Kraben/act-labs-ps1-bluetooth/ACT_Labs_REX.kicad_sch

## KiCad design ACT_Labs_REX.kicad_sch (2026-06-24)

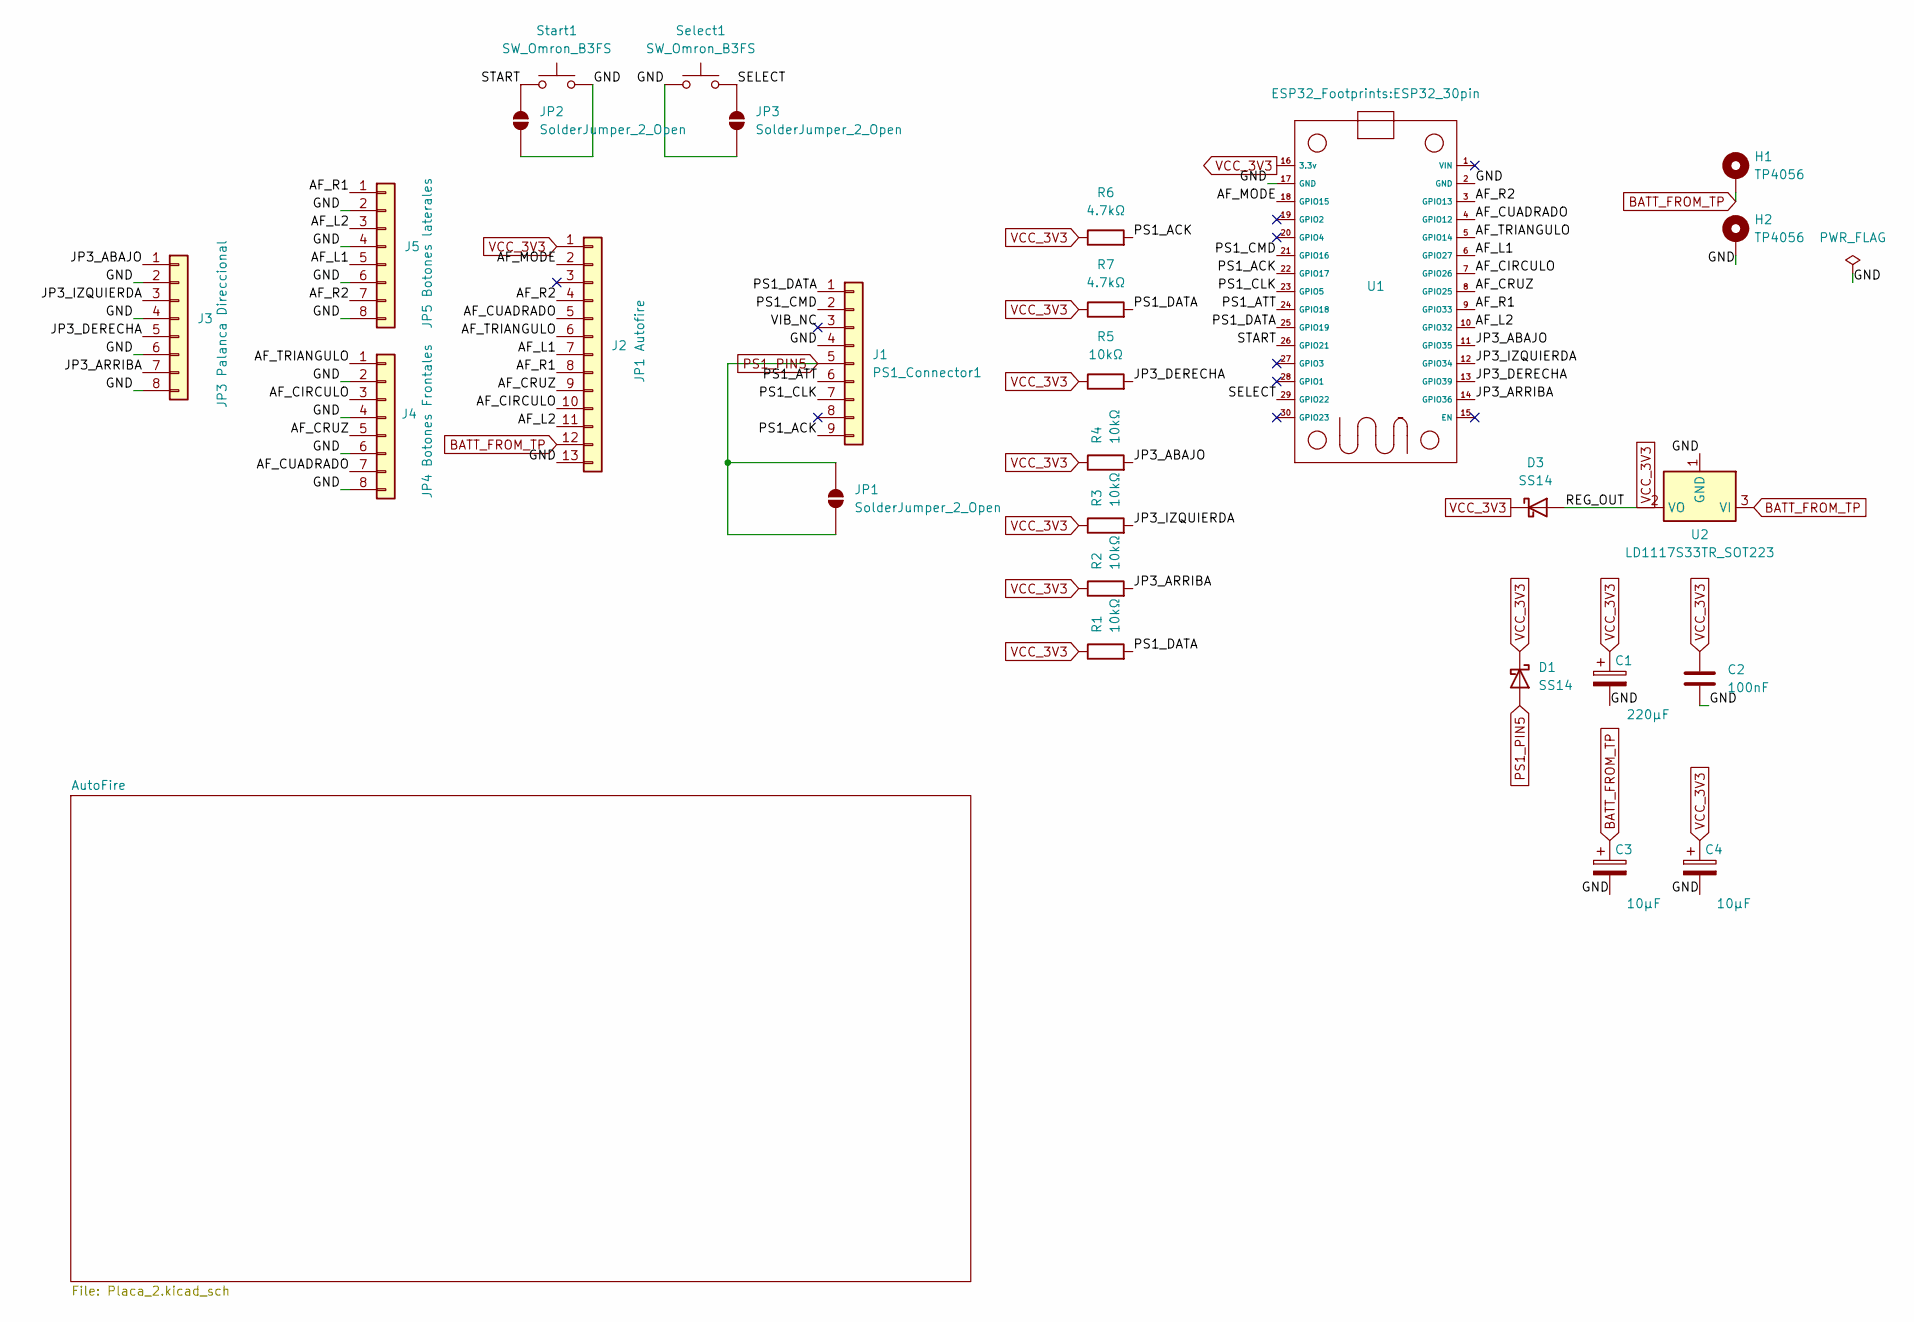
[picture p20: schematic ACT_Labs_REX.kicad_sch]

Parts:
C1: 220µF; CP_Radial_D6.3mm_P2.50mm
C2: 100nF; C_Disc_D3.0mm_W1.6mm_P2.50mm
C3, C4: 10µF; CP_Radial_D6.3mm_P2.50mm
D1, D3: SS14; D_SMA
H1, H2: TP4056; MountingHole_2.5mm_Pad
J1: PS1_Connector1; PinHeader_1x09_P2.54mm_Vertical
J2: JP1 Autofire; PinHeader_1x13_P2.54mm_Vertical
J3: JP3 Palanca Direccional; PinHeader_1x08_P2.54mm_Vertical
J4: JP4 Botones Frontales; PinHeader_1x08_P2.54mm_Vertical
J5: JP5 Botones laterales; PinHeader_1x08_P2.54mm_Vertical
JP1, JP2, JP3: SolderJumper_2_Open; SolderJumper-2_P1.3mm_Open_TrianglePad1.0x1.5mm
R1, R2, R3, R4, R5: 10kΩ; R_Axial_DIN0207_L6.3mm_D2.5mm_P7.62mm_Horizontal
R6, R7: 4.7kΩ; R_Axial_DIN0207_L6.3mm_D2.5mm_P7.62mm_Horizontal
Select1: SW_Omron_B3FS; SW_SPST_Omron_B3F-50xx
Start1: SW_Omron_B3FS; SW_SPST_Omron_B3F-50xx
U1: ESP32_30pin
U2: LD1117S33TR_SOT223; SOT-223-3_TabPin2

Connections:
AF_CIRCULO: J2.10, J4.3, U1.7 (GPIO26)
AF_CRUZ: J2.9, J4.5, U1.8 (GPIO25)
AF_CUADRADO: J2.5, J4.7, U1.4 (GPIO12)
AF_L1: J2.7, J5.5, U1.6 (GPIO27)
AF_L2: J2.11, J5.3, U1.10 (GPIO32)
AF_MODE: J2.2, U1.18 (GPIO15)
AF_R1: J2.8, J5.1, U1.9 (GPIO33)
AF_R2: J2.4, J5.7, U1.3 (GPIO13)
AF_TRIANGULO: J2.6, J4.1, U1.5 (GPIO14)
BATT_FROM_TP: C3.1, H1.1, J2.12, U2.3 (VI)
GND: C1.2, C2.2, C3.2, C4.2, H2.1, J1.4, J2.13, J3.2, J3.4, J3.6, J3.8, J4.2, J4.4, J4.6, J4.8, J5.2, J5.4, J5.6, J5.8, JP2.1 (A), JP3.1 (A), Select1.1, Start1.2, U1.2 (GND), U1.17 (GND), U2.1 (GND)
JP3_ABAJO: J3.1, R4.2, U1.11 (GPIO35)
JP3_ARRIBA: J3.7, R2.2, U1.14 (GPIO36)
JP3_DERECHA: J3.5, R5.2, U1.13 (GPIO39)
JP3_IZQUIERDA: J3.3, R3.2, U1.12 (GPIO34)
PS1_ACK: J1.9, R6.2, U1.22 (GPIO17)
PS1_ATT: J1.6, U1.24 (GPIO18)
PS1_CLK: J1.7, U1.23 (GPIO5)
PS1_CMD: J1.2, U1.21 (GPIO16)
PS1_DATA: J1.1, R1.2, R7.2, U1.25 (GPIO19)
PS1_PIN5: D1.2 (A), J1.5, JP1.1 (A), JP1.2 (B)
SELECT: JP3.2 (B), Select1.2, U1.29 (GPIO22)
START: JP2.2 (B), Start1.1, U1.26 (GPIO21)
VCC_3V3: C1.1, C2.1, C4.1, D1.1 (K), D3.1 (K), D3.2 (A), J2.1, R1.1, R2.1, R3.1, R4.1, R5.1, R6.1, R7.1, U1.16 (3.3v), U2.2 (VO)
VIB_NC: J1.3
